Makerspace-Amiens-2025-26/Otto-Groupe03/docs/images/DSC01369.JPG

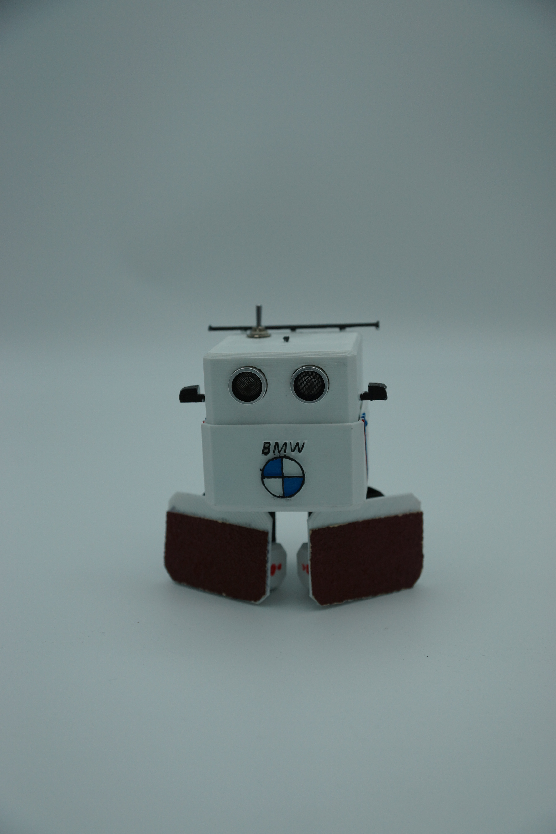
docs/images/DSC01369.JPG
